Jochen0x90h/RoomControl/software/control/src/emu/config.hpp

#pragma once


// flash
// -----

// https://infocenter.nordicsemi.com/index.jsp?topic=%2Fps_nrf52840%2Fnvmc.html&cp=4_0_0_3_2
constexpr int FLASH_PAGE_SIZE = 4096;
constexpr int FLASH_PAGE_COUNT = 16;
constexpr int FLASH_WRITE_ALIGN = 4;


// timer
// -----

constexpr int TIMER_COUNT = 4;


// calendar
// --------

constexpr int CALENDAR_SECOND_HANDLER_COUNT = 1;


// spi
// ---

constexpr int AIR_SENSOR_CS_PIN = 0;
constexpr int FERAM_CS_PIN = 1;


// display
// -------

constexpr int DISPLAY_WIDTH = 128;
constexpr int DISPLAY_HEIGHT = 64;


// radio
// -----

constexpr int RADIO_CONTEXT_COUNT = 2;
constexpr int RADIO_MAX_PAYLOAD_LENGTH = 125; // payload length without leading length byte and trailing crc
