Jochen0x90h/RoomControl/software/control/src/BusInterface.cpp

#include "BusInterface.hpp"
#include <BusMaster.hpp>
#include <Storage.hpp>
#include <Terminal.hpp>
#include <Timer.hpp>
#include <Nonce.hpp>
#include <StringOperators.hpp>
#include <Pointer.hpp>
#include <util.hpp>
#include <appConfig.hpp>


//constexpr int maxMessageLength = 64;
constexpr int micLength = 4;

// timeout to wait for a response (e.g. default response or route reply)
constexpr SystemDuration TIMEOUT = 1s;

// number of retries when a send fails
constexpr int MAX_RETRY = 2;


// BusInterface

BusInterface::BusInterface(uint8_t interfaceId, BusMaster &busMaster, Storage &storage, Storage &counters)
	: listeners(interfaceId), busMaster(busMaster), storage(storage), counters(counters)
{
	// load list of element ids
	int elementCount = sizeof(this->elementIds);
	storage.readBlocking(STORAGE_ID_BUS1, elementCount, this->elementIds);

	// load devices
	int j = 0;
	for (int i = 0; i < sizeof(this->elementIds) && i < elementCount; ++i) {
		uint8_t id = this->elementIds[i];

		// get size of stored data
		int size = storage.getSizeBlocking(STORAGE_ID_BUS1 | id);
		if (size < offsetOf(EndpointData, plugs))
			continue;

		// allocate memory and read data
		auto endpointData = reinterpret_cast<EndpointData *>(malloc(size));
		storage.readBlocking(STORAGE_ID_BUS1 | id, size, endpointData);

		// check id
		if (endpointData->id != id) {
			// id is inconsistent, delete device
			free(endpointData);
			continue;
		}

		// check size
		if (endpointData->size() != size) {
			// size is inconsistent, delete device
			free(endpointData);
			continue;
		}

		// get or load the device this endpoint belongs to
		auto *device = getOrLoadDevice(endpointData->deviceId);
		if (device == nullptr) {
			// endpoint is orphaned
			free(endpointData);
			continue;
		}

		// create endpoint, add to list of endpoints of device, device takes ownership of endpoint
		new Endpoint(this, device, endpointData);

		// device was correctly loaded
		this->elementIds[j] = id;
		++j;
	}
	this->elementCount = j;

	// load security counter
	int counterSize = 4;
	counters.readBlocking(COUNTERS_ID_BUS, counterSize, &this->securityCounter);
	if (counterSize != 4)
		this->securityCounter = 0;

	// start coroutines
	for (int i = 0; i < RECEIVE_COUNT; ++i)
		receive();
	for (int i = 0; i < PUBLISH_COUNT; ++i)
		publish();
}

BusInterface::~BusInterface() {
}

void BusInterface::setConfiguration(DataBuffer<16> const &key, AesKey const &aesKey) {
	//bool first = this->key == nullptr;
	this->key = &key;
	this->aesKey = &aesKey;
	//if (first)
	//	start();
}

String BusInterface::getName() {
	return "Bus";
}

void BusInterface::setCommissioning(bool enabled) {
	this->commissioning = enabled && this->elementCount < MAX_ELEMENT_COUNT;
	if (this->commissioning) {
	} else {
		// cancel current association coroutine if it is still running
		this->commissionCoroutine.cancel();
	}
}

Array<uint8_t const> BusInterface::getElementIds() {
	return {this->elementCount, this->elementIds};
}

String BusInterface::getName(uint8_t id) const {
	auto endpoint = getEndpoint(id);
	if (endpoint != nullptr)
		return String(endpoint->data->name);
	return {};
}

void BusInterface::setName(uint8_t id, String name) {
	auto endpoint = getEndpoint(id);
	if (endpoint != nullptr) {
		assign(endpoint->data->name, name);

		// write to flash
		this->storage.writeBlocking(STORAGE_ID_BUS1 | endpoint->data->id, endpoint->data->size(), endpoint->data);
	}
}

Array<MessageType const> BusInterface::getPlugs(uint8_t id) const {
	auto endpoint = getEndpoint(id);
	if (endpoint != nullptr)
		return {endpoint->data->plugCount, endpoint->data->plugs};
	return {};
}

SubscriberTarget BusInterface::getSubscriberTarget(uint8_t id, uint8_t plugIndex) {
	auto endpoint = getEndpoint(id);
	if (endpoint != nullptr && plugIndex < endpoint->data->plugCount)
		return {endpoint->data->plugs[plugIndex], &this->publishBarrier};
	return {};
}

void BusInterface::subscribe(Subscriber &subscriber) {
	subscriber.remove();
	if (subscriber.target.barrier == nullptr)
		return;
	auto id = subscriber.data->source.elementId;
	auto endpoint = getEndpoint(id);
	if (endpoint != nullptr)
		endpoint->subscribers.add(subscriber);
}

void BusInterface::listen(Listener &listener) {
	assert(listener.barrier	!= nullptr);
	listener.remove();
	this->listeners.add(listener);
}

void BusInterface::erase(uint8_t id) {
	auto d = &this->devices;
	while (*d != nullptr) {
		auto device = *d;

		// iterate over endpoints (each endpoint is exposed as a device)
		auto e = &device->endpoints;
		while (*e != nullptr) {
			auto endpoint = *e;
			if (endpoint->data->id == id) {
				// remove endpoint from linked list
				*e = endpoint->next;

				// check if device has no endpoints left
				if (device->endpoints == nullptr) {
					// remove device from linked list
					*d = device->next;

					// erase device from flash
					this->storage.eraseBlocking(STORAGE_ID_BUS2 | device->data.id);

					// delete device
					delete device;
				}

				// erase endpoint from flash
				this->storage.eraseBlocking(STORAGE_ID_BUS1 | id);

				// delete endpoint
				delete endpoint;

				goto list;
			}
		}
		d = &device->next;
	}

list:

	// erase from list of device id's
	this->elementCount = eraseElement(this->elementCount, this->elementIds, id);
	this->storage.writeBlocking(STORAGE_ID_BUS1, this->elementCount, this->elementIds);
}

// private:

// Device
BusInterface::Device::Device(BusInterface *interface, DeviceData const &data)
	: next(interface->devices), data(data)
{
	interface->devices = this;

	// load security counter
	int counterSize = 4;
	interface->counters.readBlocking(COUNTERS_ID_BUS + data.id, counterSize, &this->securityCounter);
	if (counterSize != 4)
		this->securityCounter = 0;
}

BusInterface::Device::~Device() {
	// delete endpoints
	auto endpoint = this->endpoints;
	while (endpoint != nullptr) {
		auto e = endpoint;
		endpoint = endpoint->next;
		delete e;
	}
}

// Endpoint
BusInterface::Endpoint::~Endpoint() {
	free(this->data);
}

BusInterface::Endpoint *BusInterface::getEndpoint(uint8_t id) const {
	auto device = this->devices;
	while (device != nullptr) {
		auto endpoint = device->endpoints;
		while (endpoint != nullptr) {
			if (endpoint->data->id == id)
				return endpoint;
			endpoint = endpoint->next;
		}
		device = device->next;
	}
	return nullptr;
}

uint8_t BusInterface::allocateId(int elementCount) {
	// find a free id
	int id;
	for (id = 1; id < 256; ++id) {
		for (int j = 0; j < elementCount; ++j) {
			if (this->elementIds[j] == id)
				goto found;
		}
		break;
	found:;
	}
	return id;
}

uint8_t BusInterface::allocateDeviceId() {
	// find a free id
	int id;
	for (id = 1; id < 256; ++id) {
		auto device = this->devices;
		while (device != nullptr) {
			if (device->data.id == id)
				goto found;
			device = device->next;
		}
		break;
	found:;
	}
	return id;
}

BusInterface::Device *BusInterface::getOrLoadDevice(uint8_t deviceId) {
	auto device = this->devices;
	while (device != nullptr) {
		if (device->data.id == deviceId)
			return device;
		device = device->next;
	}

	// load data
	DeviceData data;
	int size = sizeof(data);
	this->storage.readBlocking(STORAGE_ID_BUS2 | deviceId, size, &data);
	if (size != sizeof(data))
		return nullptr;

	// check id
	if (data.id != deviceId)
		return nullptr;

	// create device
	return new Device(this, data);
}


/*
static bool readMessage(MessageType dstType, void *dstMessage, MessageType srcType, MessageReader r,
	ConvertOptions const &convertOptions)
{
	auto &dst = *reinterpret_cast<Message *>(dstMessage);

	switch (srcType & MessageType::CATEGORY) {
	case MessageType::BINARY:
	case MessageType::TERNARY:
		return convertSwitch(dstType, dst, r.u8(), convertOptions);
	case MessageType::MULTISTATE:
		// todo
		break;
	/ *case MessageType::LEVEL: {
		// level: convert from 0 - 65535 to 0.0 - 1.0
		float level = float(r.u16L()) / 65535.0f;
		if ((srcType & MessageType::CMD) == 0)
			return convertFloat(dstType, dst, level, convertOptions);
		uint8_t command = r.u8();
		if (command > 1) {
			// negative step
			command = 1;
			level = -level;
		}
		return convertFloatCommand(dstType, dst, command, level, convertOptions);
	}* /
	case MessageType::LEVEL:
	case MessageType::PHYSICAL:
	case MessageType::CONCENTRATION: {
		float value = r.f32L();
		if ((srcType & MessageType::CMD) == 0)
			return convertFloat(dstType, dst, value, convertOptions);
		uint8_t command = r.u8();
		return convertFloatCommand(dstType, dst, value, command, convertOptions);
	}
	case MessageType::LIGHTING: {
		float value = r.f32L();
		if ((srcType & MessageType::CMD) == 0)
			return convertFloat(dstType, dst, value, convertOptions);
		uint8_t command = r.u8();
		uint16_t transition = r.u16L();
		return convertFloatTransition(dstType, dst, value, command, transition, convertOptions);
/ *
		// lighting: all values are normalized except color temperature
		float value = r.u16L();
		if ((srcType & MessageType::LIGHTING_CATEGORY) != MessageType::LIGHTING_COLOR_TEMPERATURE)
			value /= 65535.0f;
		if ((srcType & MessageType::CMD) == 0)
			return convertFloat(dstType, dst, value, convertOptions);
		uint8_t command = r.u8();
		uint16_t transition = r.u16L();
		return convertFloatTransition(dstType, dst, value, command, transition, convertOptions);
* /
	}
	case MessageType::METERING:
		// todo
	default:
		// conversion failed
		return false;
	}

	// conversion successful
	return true;
}*/

Coroutine BusInterface::receive() {
	uint8_t receiveMessage[MESSAGE_LENGTH];

	while (true) {
		int receiveLength = MESSAGE_LENGTH;
		co_await this->busMaster.receive(receiveLength, receiveMessage);

		// debug print received message
		//for (int i = 0; i < receiveLength; ++i)
		//	Terminal::out << hex(receiveMessage[i]) << ' ';
		//Terminal::out << '\n';

		bus::MessageReader r(receiveLength, receiveMessage);

		// set start of header
		r.setHeader();

		// get address
		if (r.peekU8() == 0) {
			// 0: enumerate message (device wants to be commissioned)
			r.u8();

			// check if commissioning of new devices is allowed
			if (!this->commissioning)
				continue;

			// get encoded bus device id
			uint32_t busDeviceId = r.id();

			// check message integrity code (mic)
			r.setMessageFromEnd(micLength);
			Nonce nonce(busDeviceId, 0);
			if (!r.decrypt(micLength, nonce, bus::defaultAesKey))
				continue;

			// protocol version
			auto version = r.u8();

			// endpoint count
			int endpointCount = r.u8();

			// cancel current association coroutine
			this->commissionCoroutine.cancel();

			// restrict maximum number of devices (each endpoint counts as one device)
			//endpointCount = min(endpointCount, MAX_ELEMENT_COUNT - this->elementCount);

			// handle commissioning
			//if (endpointCount > 0)
			this->commissionCoroutine = handleCommission(busDeviceId, endpointCount);
		} else {
			// data message

			// get address
			uint8_t address = r.address();

			// get security counter
			uint32_t securityCounter = r.u32L();
			//Terminal::out << "device " << dec(address) << " security counter " << hex(securityCounter) << '\n';

			// set start of encrypted message
			r.setMessage();

			// decrypt
			Nonce nonce(address, securityCounter);
			if (!r.decrypt(micLength, nonce, *this->aesKey)) {
				Terminal::out << "bus: decrypt failed!\n";
				continue;
			}

			// get endpoint index
			uint8_t endpointIndex = r.u8();
			if (endpointIndex == 255) {
				// attribute data
				endpointIndex = r.u8();

				// check if there is a device in the commissioning process
				if (this->commissionCoroutine.isAlive() && this->tempDevice->data.address == address) {
					// check security counter
					if (securityCounter <= this->tempDevice->securityCounter) {
						Terminal::out << "B security counter error " << dec(securityCounter) << " <= " << dec(this->tempDevice->securityCounter) << '\n';
						//continue;
					} else {
						//Terminal::out << "B security counter ok " << dec(securityCounter) << " > " << dec(this->tempDevice->securityCounter) << '\n';
					}
					this->tempDevice->securityCounter = securityCounter;

					// resume commissioning coroutine via responseBarrier
					auto attribute = r.e8<bus::Attribute>();
					int length = min(r.getRemaining(), MESSAGE_LENGTH);
					uint8_t *response = r.current;
					this->responseBarrier.resumeFirst(
						[address, endpointIndex, attribute, length, response](Response &r) {
							if (r.address == address && r.endpointIndex == endpointIndex && r.attribute == attribute) {
								r.length = length;
								array::copy(length, r.response, response);
								return true;
							}
							return false;
						});
				}
			} else {
				// search device with address
				auto device = this->devices;
				while (device != nullptr) {
					if (device->data.address != address) {
						device = device->next;
						continue;
					}

					// check security counter
					if (securityCounter <= device->securityCounter) {
						Terminal::out << 'B' << dec(device->data.busDeviceId) << ": security counter error " << dec(securityCounter) << " <= " << dec(device->securityCounter) << '\n';
						//break;
					} else {
						//Terminal::out << 'B' << dec(device->data.busDeviceId) << ": security counter ok " << dec(securityCounter) << " > " << dec(device->securityCounter) << '\n';
					}
					device->securityCounter = securityCounter;

					// store security counter
					Storage::Status status;
					co_await this->counters.write(COUNTERS_ID_BUS + device->data.id, 4, &securityCounter, status);
					//this->counters.writeBlocking(COUNTERS_ID_BUS + device->data.id, 4, &securityCounter);

					// search endpoint with index
					auto endpoint = device->endpoints;
					while (endpoint != nullptr) {
						if (endpointIndex > 0) {
							--endpointIndex;
							endpoint = endpoint->next;
							continue;
						}

						// get plug index
						uint8_t plugIndex = r.u8();

						// publish to subscribers
						auto srcType = endpoint->data->plugs[plugIndex];
						switch (srcType & MessageType::CATEGORY) {
						case MessageType::BINARY:
						case MessageType::TERNARY: {
							uint8_t value = r.u8();
							endpoint->publishSwitch(plugIndex, value);
							break;
						}
						case MessageType::MULTISTATE:
							// todo
							break;
						case MessageType::LEVEL:
						case MessageType::PHYSICAL:
						case MessageType::CONCENTRATION: {
							float value = r.f32L();
							if ((srcType & MessageType::CMD) == 0) {
								endpoint->publishFloat(plugIndex, value);
							} else {
								uint8_t command = r.u8();
								endpoint->publishFloatCommand(plugIndex, value, command);
							}
							break;
						}
						case MessageType::LIGHTING: {
							float value = r.f32L();
							if ((srcType & MessageType::CMD) == 0) {
								endpoint->publishFloat(plugIndex, value);
							} else {
								uint8_t command = r.u8();
								uint16_t transition = r.u16L();
								endpoint->publishFloatTransition(plugIndex, value, command, transition);
							}
							break;
						}
						case MessageType::METERING:
							// todo
							break;
						default:;
						}

						// finished with endpoint
						break;
					}

					// finished with device
					break;
				}
			}
		}
	}
}

AwaitableCoroutine BusInterface::handleCommission(uint32_t busDeviceId, uint8_t endpointCount) {
	// find existing device if any
	auto od = &this->devices;
	while (*od != nullptr) {
		auto device = *od;
		if (device->data.busDeviceId == busDeviceId)
			break;
		od = &device->next;
	}
	auto oldDevice = *od;

	// check if we are out of space for new devices
	bool outOfDevices = oldDevice == nullptr && this->elementCount >= MAX_ELEMENT_COUNT;

	// variables
	int length;
	uint8_t message[MESSAGE_LENGTH];

	// create new bus device
	DeviceData deviceData;
	deviceData.id = oldDevice != nullptr ? oldDevice->data.id : allocateDeviceId();
	deviceData.address = deviceData.id - 1;
	deviceData.busDeviceId = busDeviceId;

	// check if out of addresses
	if (deviceData.address > LAST_ADDRESS || outOfDevices)
		co_return; // todo: maybe send a commissioning message with failed status (e.g. no address and key)

	// use Pointer in case the coroutine gets cancelled
	Pointer<Device> device = new Device(deviceData);

	// set pointer so that we can forward responses
	this->tempDevice = device.ptr;

	// send commissioning message
	{
		bus::MessageWriter w(message);

		// set start of header
		w.setHeader();

		// command prefix
		w.u8(0);

		// arbitration byte that always "wins" against enumeration messages sent by devices
		w.u8(0);

		// device id
		w.u32L(busDeviceId);

		// address that gets assigned to the device (use storage id)
		w.u8(deviceData.address);

		// key
		w.data8(*this->key);

		// only add message integrity code (mic) using default key, message stays unencrypted
		w.setMessage();
		Nonce nonce(busDeviceId, 0);
		w.encrypt(micLength, nonce, bus::defaultAesKey);

		length = w.getLength();
	}
	co_await this->busMaster.send(length, message);


	// configure endpoints
	Endpoint *oldEndpoint = oldDevice != nullptr ? oldDevice->endpoints : nullptr;
	int elementCount = this->elementCount;
	for (uint8_t endpointIndex = 0; endpointIndex < endpointCount; ++endpointIndex) {
		// check if we have space for a new element (each endpoint is an element)
		if (oldEndpoint == nullptr && elementCount >= MAX_ELEMENT_COUNT)
			continue;

		// get plug list
		co_await readAttribute(length, message, *device, endpointIndex, bus::Attribute::PLUG_LIST);
		if (length == -1)
			co_return;
		int plugCount = length / 2;

		// allocate endpoint data
		auto data = reinterpret_cast<EndpointData *>(malloc(offsetOf(EndpointData, plugs[plugCount])));

		// set plugs
		data->plugCount = plugCount;
		MessageReader plugs(length, message);
		for (int i = 0; i < plugCount; ++i) {
			data->plugs[i] = plugs.e16L<MessageType>();
			Terminal::out << dec(endpointIndex) << " " << getTypeLabel(data->plugs[i]) << "\n";
		}

		// set id
		if (oldEndpoint != nullptr) {
			// reuse id from old endpoint
			data->id = oldEndpoint->data->id;
		} else {
			// allocate new id
			data->id = allocateId(elementCount);
			this->elementIds[elementCount++] = data->id;
		}

		// set device id
		data->deviceId = device->data.id;

		// get name
		co_await readAttribute(length, message, *device, endpointIndex, bus::Attribute::MODEL_IDENTIFIER);
		if (length > 0)
			assign(data->name, String(length, message));
		else
			assign(data->name, "Device");

		// create endpoint, add to list of endpoints of device, device takes ownership of endpoint
		new Endpoint(this, device.ptr, data);

		if (oldEndpoint != nullptr)
			oldEndpoint = oldEndpoint->next;
	}

	// remove remaining old endpoints from device list
	while (oldEndpoint != nullptr) {
		elementCount = eraseElement(elementCount, this->elementIds, oldEndpoint->data->id);
		oldEndpoint = oldEndpoint->next;
	}

	// delete old device
	if (oldDevice != nullptr) {
		// remove device from linked list
		*od = oldDevice->next;

		// move subscribers from old to new endpoints
		auto oldEndpoint = oldDevice->endpoints;
		auto endpoint = device->endpoints;
		while (oldEndpoint != nullptr && endpoint != nullptr) {
			//endpoint->subscribers.add(static_cast<Subscriber &>(static_cast<LinkedListNode<Subscriber> &>(oldEndpoint->subscribers)));
			endpoint->subscribers.add(oldEndpoint->subscribers); // only works because old list removes itself from linked list
			oldEndpoint = oldEndpoint->next;
			endpoint = endpoint->next;
		}

		// delete old device and its endpoints
		delete oldDevice;
	}

	// store list of device id's (each endpoint is treated as a device)
	this->elementCount = elementCount;
	this->storage.writeBlocking(STORAGE_ID_BUS1, elementCount, this->elementIds);

	// check if device has any endpoints
	if (device->endpoints == nullptr)
		co_return;

	// store security counter
	this->counters.writeBlocking(COUNTERS_ID_BUS + device->data.id, 4, &device->securityCounter);

	// store endpoints
	auto endpoint = device->endpoints;
	while (endpoint != nullptr) {
		this->storage.writeBlocking(STORAGE_ID_BUS1 | endpoint->data->id, endpoint->data->size(), endpoint->data);
		endpoint = endpoint->next;
	}

	// store device
	this->storage.writeBlocking(STORAGE_ID_BUS2 | device->data.id, sizeof(device->data), &device->data);

	// transfer ownership of device to devices list
	device->next = this->devices;
	this->devices = device.ptr;
	device.ptr = nullptr;
}

AwaitableCoroutine BusInterface::readAttribute(int &length, uint8_t (&message)[MESSAGE_LENGTH], Device &device,
	uint8_t endpointIndex, bus::Attribute attribute)
{
	for (int retry = 0; ; ++retry) {
		// request attribute
		{
			bus::MessageWriter w(message);

			// set start of header
			w.setHeader();

			// encoded address
			w.address(device.data.address);

			// security counter
			w.u32L(this->securityCounter);

			// set start of message
			w.setMessage();

			// "escaped" endpoint index
			w.u8(255);
			w.u8(endpointIndex);

			// attribute
			w.e8(attribute);

			// no message data to indicate that we want to read the attribute

			// encrypt
			Nonce nonce(device.data.address, this->securityCounter);
			w.encrypt(micLength, nonce, *this->aesKey);

			length = w.getLength();
		}

		// increment and store security counter
		++this->securityCounter;
		Storage::Status status;
		co_await this->counters.write(COUNTERS_ID_BUS, 4, &this->securityCounter, status);

		// send
		co_await this->busMaster.send(length, message);

		// wait for a response from the device
		int r = co_await select(
			this->responseBarrier.wait(length, message, device.data.address, endpointIndex, attribute),
			Timer::sleep(TIMEOUT));

		// check if response was received
		if (r == 1)
			break;

		if (retry == MAX_RETRY) {
			length = -1;
			co_return;
		}
	}
}

static bool writeMessage(MessageWriter &w, MessageType type, Message &message) {
	switch (type & MessageType::CATEGORY) {
	case bus::PlugType::BINARY:
	case bus::PlugType::TERNARY:
		//Terminal::out << "message " << dec(message.value.u8) << '\n';
		w.u8(message.value.u8);
		break;
	case MessageType::MULTISTATE:
		// todo
		break;
	/*case MessageType::LEVEL: {
		float value = message.value.f;
		uint8_t cmd = 0;
		if ((type & MessageType::CMD) != 0) {
			cmd = message.command;
			if (value < 0 && cmd != 0) {
				value = -value;
				cmd = 2;
			}
		}
		w.u16L(clamp(int(value * 65535.0f + 0.5f), 0, 65535));
		if ((type & MessageType::CMD) != 0)
			w.u8(cmd);
		break;
	}*/
	case MessageType::LEVEL:
	case MessageType::PHYSICAL:
	case MessageType::CONCENTRATION:
		w.f32L(message.value.f32);
		if ((type & MessageType::CMD) != 0)
			w.u8(message.command);
		break;
	case MessageType::LIGHTING: {
		w.f32L(message.value.f32);
		if ((type & MessageType::CMD) != 0) {
			w.u8(message.command);
			w.u16L(message.transition);
		}
		break;
/*
		float value = message.value.f;
		if ((type & MessageType::LIGHTING_CATEGORY) != MessageType::LIGHTING_COLOR_TEMPERATURE)
			value *= 65535.0f;
		w.u16L(clamp(int(value + 0.5f), 0, 65535));
		if ((type & MessageType::CMD) != 0) {
			w.u8(message.command);
			w.u16L(message.transition);
		}
		break;*/
	}
	case MessageType::METERING:
		// todo
		break;
	default:
		// not supported
		return false;
	}
	return true;
}

Coroutine BusInterface::publish() {
	uint8_t sendMessage[MESSAGE_LENGTH];
	while (true) {
		// wait for message
		SubscriberInfo info;
		Message message;
		co_await this->publishBarrier.wait(info, &message);
		//Terminal::out << "BusInterface::publish() sourceIndex " << dec(info.sourceIndex) << " deviceId " << dec(info.deviceId) << " plugIndex " << dec(info.plugIndex) << '\n';

		// find destination device
		auto device = this->devices;
		while (device != nullptr) {
			auto endpoint = device->endpoints;
			int endpointIndex = 0;
			while (endpoint != nullptr) {
				if (endpoint->data->id != info.elementId) {
					endpoint = endpoint->next;
					++endpointIndex;
					continue;
				}

				// get plug info
				uint8_t plugIndex = info.plugIndex;
				if (plugIndex >= endpoint->data->plugCount)
					break;
				auto messageType = endpoint->data->plugs[plugIndex];

				// check if it is an output
				if (isInput(messageType)) {
					// send data message to node
					int length;
					{
						bus::MessageWriter w(sendMessage);

						// set start of header
						w.setHeader();

						// encoded device address
						w.address(device->data.address);

						// security counter
						w.u32L(this->securityCounter);

						// set start of message
						w.setMessage();

						// endpoint index
						w.u8(endpointIndex);

						// plug index
						w.u8(plugIndex);

						// message data
						if (!writeMessage(w, messageType, message))
							break;

						// encrypt
						Nonce nonce(device->data.address, this->securityCounter++);
						w.encrypt(micLength, nonce, *this->aesKey);

						length = w.getLength();
					}

					// store security counter
					Storage::Status status;
					co_await this->counters.write(COUNTERS_ID_BUS, 4, &this->securityCounter, status);

					// send
					co_await this->busMaster.send(length, sendMessage);
				}

				/*
				// forward to subscribers
				for (auto &subscriber: device.subscribers) {
					if (subscriber.index == publisher.index) {
						subscriber.barrier->resumeAll([&subscriber, &publisher](Subscriber::Parameters &p) {
							p.subscriptionIndex = subscriber.subscriptionIndex;

							// convert to target unit and type and resume coroutine if conversion was successful
							return convert(subscriber.messageType, p.message,
								publisher.messageType, publisher.message);
						});
					}
				}*/

				break;
			}
			if (endpoint != nullptr)
				break;
			device = device->next;
		}
	}
}
